keefo/open-plant-pulse/docs/hub.md

# Open Plant Pulse hub

## Goal and priorities

Open Plant Pulse has one hub project: the Python service in [`hub/`](../hub/).
The hub has two primary responsibilities:

1. Run a BLE/BTHome subscriber that continuously listens for nearby sensor
   advertisements, validates them, and stores readings in SQLite.
2. Host a local HTTP server where household users can discover, name, manage, and
   monitor sensors and plants through a web browser.

BLE/BTHome ingestion is the first sensor transport. The HTTP server is still a
core product surface, but it initially serves the hub-owned web application and
only the internal endpoints needed by that application. A stable public HTTP API,
sensor-to-hub Wi-Fi/HTTP reporting, MQTT, and other integrations are lower-priority
follow-up work.

> [!IMPORTANT]
> BTHome advertisements remain one-way telemetry. Firmware 0.3.0 adds a separate,
> bounded connected-BLE service: after the next report, the hub can send plant name,
> room, and reporting interval and verify them by read-back. The prototype service
> is unauthenticated and must not be treated as secure provisioning.

The checked-in vertical slice serves a standard-library HTTP dashboard. It also
includes a Bleak BTHome subscriber,
stable sensor-owned identity, report deduplication, deterministic replay, explicit
SQLite migrations, partial-source storage, and separate scanner/database health.
These paths are host-tested with captured advertisements. The browser now includes
hub health, an unclaimed-sensor inbox, an enrolled fleet overview, sensor-scoped
monitoring, and hub-owned management workflows. CoreBluetooth discovery and scanner
startup have been exercised on macOS; physical BTHome reception and Linux remain
unvalidated.

## Target architecture

```mermaid
flowchart LR
    Probe[RS485 soil probe] --> Sensor[Battery sensor node]
    Air[SHT45 air sensor] --> Sensor
    Sensor -->|BTHome v2 advertisements| BLE[Hub BLE subscriber]
    BLE --> Ingest[Ingestion and enrollment]
    Ingest --> DB[(SQLite)]
    DB --> Web[Local HTTP server and web UI]
    User[Household user] <-->|manage and monitor| Web
    Sensor -.->|same BTHome advertisements| HA[Home Assistant]
    DB -.->|later MQTT bridge| HA
    DB -.->|later public HTTP API| Clients[External clients]
```

The hub remains one background service and one operational SQLite database. The
BLE subscriber and HTTP server run independently: a browser or downstream client
failure must not stop collection, and a temporary Bluetooth failure must not make
stored history unavailable.

Reliable BLE ingestion and persistence take priority over dashboard polish,
analytics, public APIs, MQTT, notifications, and other downstream capabilities.
The implementation should extend the current `sqlite3` store and standard-library
`ThreadingHTTPServer` before adding another framework or storage abstraction.

## Technology baseline

| Concern | Baseline | Reason |
| --- | --- | --- |
| Runtime | Python 3.9+ | Supported by the existing package |
| Sensor ingestion | Passive BTHome v2 advertisements over BLE | Low sensor wake-cycle energy and no Wi-Fi association |
| BLE adapter | `bleak` | Already declared; supports macOS CoreBluetooth and Linux BlueZ |
| HTTP service | Python standard-library threaded server initially | Already powers the tested browser slice |
| Store | SQLite through Python `sqlite3` | Embedded, transactional, and already implemented |
| Home Assistant | Direct BTHome first; hub MQTT later | The same broadcast can be heard without coupling HA to the hub |
| Tests | `unittest` baseline; `pytest` development extra | Zero-dependency core checks and optional richer tooling |

The store uses standard-library `sqlite3`; do not introduce asynchronous database
access unless the BLE runtime demonstrates a need for it. Keep Bluetooth callbacks
short: normalize an advertisement and hand it to application/storage code without
blocking the scanner.

## Current development setup

From the repository root:

```sh
python3 -m venv .venv
. .venv/bin/activate
python3 -m pip install -e './hub[dev]'
pytest hub/tests
```

The current contract and hub tests need no installation:

```sh
PYTHONPATH=hub/src python3 -m unittest discover -s hub/tests
```

Run the existing vertical slice:

```sh
PYTHONPATH=hub/src python3 -m open_plant_pulse_hub
```

Visit <http://localhost/>, or the computer's own name such as
`http://imac.local/`. Readings arrive from BTHome sensors in range.

The interface listens on port 80 on every address, over IPv4 and IPv6, so either
family a name resolves to reaches it. It answers only the computer it runs on and
refuses other computers with 403: it has no login, and macOS lets an ordinary
user take port 80 only on every address at once, so the limit is kept per
request rather than by binding to loopback. `--allow-network` lets the household
network in; `--host` and `--port` choose another address or port.

Firmware images are served separately on `0.0.0.0:8081`, because a sensor
downloads an update over the household network and cannot reach loopback. That
server answers one shape of request — `GET /firmware/<sha256>.bin` — and holds
nothing private. `--firmware-host`, `--firmware-port` and `--no-firmware-server`
change or disable it.

### Running as a macOS service

`deploy/launchd/install.sh` installs the hub as a LaunchAgent that starts at
login and restarts if it exits. It runs the checkout it sits in, through an
ad-hoc signed app bundle, `~/Applications/Open Plant Pulse Hub.app`: a bare
launchd process has no code identity for macOS to attribute Bluetooth
permission to, and its scanner then stays `stopped` without an error. The
bundle's main executable is a small compiled launcher (`launcher.c`, built by
the script, so it needs the Xcode command line tools) that runs the hub as its
child: local network privacy, which grow light control needs, refuses every LAN
connection from an app whose main executable is a script, with `No route to
host` and no prompt. The first light command asks for Local Network permission;
it is under System Settings › Privacy & Security › Local Network. Run the
script again after changing the launcher or moving the checkout, since that
re-signs the bundle; `uninstall.sh` removes the agent and the bundle and keeps
the database. Logs go to `~/Library/Logs/open-plant-pulse/`. Python changes
need a restart, `launchctl kickstart -k gui/$(id -u)/com.openplantpulse.hub`;
the page's own files are read from disk on every request and need none.

### Reaching the hub away from home

Use Tailscale Serve rather than opening a port on the router: the interface has
no login, and anyone who reaches it can reconfigure sensors and install
firmware. With Tailscale on the hub computer and on each phone or laptop that
should reach it, `tailscale serve --bg 80` publishes the page at
`https://<computer>.<tailnet>.ts.net` to those devices only, with a certificate
Tailscale renews. Serve relays through the hub computer, so the hub counts every
such request as local and Tailscale's sign-in is the only access control: never
turn on Funnel or a public tunnel without an authentication layer in front, and
never serve the firmware port. A Serve setting belongs to the computer's
Tailscale name; after renaming the computer, run `tailscale serve reset` and
serve again.

The hub exposes these implementation endpoints for its current page:

- `GET /api/health`
- `GET /api/sensors?status=unclaimed|enrolled|archived`
- `GET /api/sensors/<sensor-id>`
- `GET /api/settings`
- `GET /api/readings/latest`
- `GET /api/readings/history`
- `GET /api/care-log`
- `GET /api/raw-reports?sensor_id=<sensor-id>` (temporary debugging surface)
- `PUT /api/sensors/<sensor-id>`
- `PUT /api/sensors/<sensor-id>/name`
- `PUT /api/sensors/profile`
- `PUT /api/settings`
- `DELETE /api/sensors/<sensor-id>`
- `POST /api/sensors/<sensor-id>/archive`
- `POST /api/sensors/<sensor-id>/replace`
- `GET /api/firmware`
- `POST /api/firmware` (the image itself as the request body)
- `POST /api/sensors/<sensor-id>/firmware` (a digest to install, or none to stop)
- `DELETE /api/firmware/<sha256>`

These routes are an internal browser contract, not the promised public HTTP API.
They may evolve as the multi-sensor UI is built. State-changing routes reject a
browser `Origin` that does not match the request `Host`; requests without `Origin`
remain available to local command-line tools. The server binds to loopback unless
`--host` is explicitly supplied. For LAN use, bind to a private interface only,
restrict the port with the host firewall, and do not expose it to the Internet.
Deterministic BLE tests use the advertisement replay adapter with
[`protocol/fixtures/bthome-v3-replay.json`](../protocol/fixtures/bthome-v3-replay.json).

### Native Bluetooth setup

Install the hub in the repository virtual environment before using BLE:

```sh
python3 -m venv .venv
. .venv/bin/activate
python3 -m pip install -e './hub[dev]'
```

On macOS, Bleak uses CoreBluetooth. The first scan should prompt for Bluetooth
access; if access was denied, enable the terminal or packaged hub under **System
Settings → Privacy & Security → Bluetooth**. A future bundled application must
include `NSBluetoothAlwaysUsageDescription` in its `Info.plist`. CoreBluetooth
reports host-scoped UUIDs rather than portable Bluetooth addresses, which is why
the hub does not use them as sensor identity.

On Linux, Bleak communicates with BlueZ over the system D-Bus. Ensure BlueZ is
installed, the Bluetooth service and adapter are enabled, and the service account
can access the system D-Bus and BlueZ discovery APIs. Do not run the hub as root as
a substitute for correct service permissions. Container or user-namespace
deployment needs explicit D-Bus and adapter access and remains unvalidated.

Start the hub and inspect scanner/database state independently:

```sh
open-plant-pulse-hub
curl --fail --silent http://localhost/api/health
```

`scanner.status` should become `scanning`; permission or adapter failures appear as
`unavailable` with `last_error`. `last_receive_at` remains null until a supported
`0xFCD2` advertisement has decoded successfully. `database.status` reports SQLite
health separately. Use `--no-ble` only when intentionally disabling collection.

## BLE/BTHome subscriber design

### Scan behavior

The subscriber must:

- use observation-only scanning for telemetry; Bleak's active discovery mode remains
  enabled so the `sensor-<DEVICE_ID>` local-name scan response is available on macOS
  and Linux;
- filter service data for BTHome UUID `0xFCD2` in the discovery callback before
  decoding; do not use a scanner-level service UUID filter because CoreBluetooth
  suppresses the sensor's valid service-data-only advertisements when it is set;
- accept only contract-v3 packets: BTHome v2 service data with unencrypted
  device info and the packet 1, packet 2, or beacon layout;
- record the hub receipt time, source adapter, observed Bluetooth identifier, and
  RSSI when the platform provides them;
- reject malformed or unsupported advertisements without stopping the scan loop;
- reconnect with bounded backoff after adapter loss; and
- expose scanner state and the last successful advertisement time to hub health.

For an enrolled sensor with pending device configuration, the subscriber opens one
bounded GATT connection using the platform-observed identifier, writes the versioned
payload, and reads it back. Matching bytes acknowledge application; connection,
write, or read-back failures remain visible as retrying and are attempted on a later
report. The hub records the sensor's reporting interval only from that matching
read-back; saving a new hub interval leaves the last confirmed sensor interval
unchanged until synchronization succeeds. The hub does not connect when no
configuration is pending and no drain is due.

An enrolled sensor keeps each report in a flash queue until the hub acknowledges
it, and advertises its newest queued report the moment it is made. The hub stores
that report straight from the advertisement, which is what keeps the page fresh at
the reporting interval. The queue itself is moved by a bulk drain (see
[durable delivery](../protocol/README.md#durable-delivery-and-acknowledgement)):
over one bonded connection on the same characteristic the hub writes the drain
request `20`, reads queue pages (`20`, a count of up to eight, then each report's
ID and its two advertised packets), stores every report through the same
ingestion path, duplicate and conflict rules as advertised packets, writes the
cumulative acknowledgement `21` plus the last stored report ID (unsigned 32-bit
little-endian), and repeats until a page is empty, then writes the end token
`22`. Drained packets appear in the raw report log with source adapter
`bleak-drain`, the drain time as receipt time and the connection's identifier.

A drain pauses the sensor's advertising for a couple of seconds, so it is the
background guarantee rather than the freshness path. On hearing a packet of a
report that is not yet acknowledged, from a sensor it owns, the subscriber drains
when:

- it has not drained that sensor since the hub started;
- a report ID between the last acknowledged report and this one is not held
  complete, meaning a report was missed over the air; or
- 30 seconds (`DRAIN_INTERVAL_SECONDS`) have passed since the sensor's last
  successful drain.

That decides whether a drain is due, not when it starts. A due drain waits until
the report just heard is complete (both packets stored), which is the start of
the quiet part of the sensor's reporting cycle: the connection then pauses
advertising after a fresh report was heard instead of across it. If no report
completes over the air within 10 seconds (`DRAIN_DEFER_LIMIT_SECONDS`), it drains
anyway. While a drain waits, configuration, status and update work wait with it
and ride on its connection.

Drains of one sensor never overlap and start at most every two seconds
(`DRAIN_SPACING_SECONDS`), whatever the outcome of the last. A failed drain
(connection error, a refused page) is simply tried again by the next
advertisement. One connection reads at most 16 pages (128 reports), and stops
early if a page begins with a report it has already acknowledged. Pending
configuration, a station status poll and a firmware update command share the drain
connection and go before the drain request; a pending release still goes first,
on its own connection.

A page is decoded strictly: a wrong marker, more than eight reports, truncated or
trailing bytes, a record whose ID is not the one inside its packets, packets that
are not a valid packet 1 and packet 2 pair, or reports out of order refuse the
whole page, acknowledging nothing. A report in conflict, or one with any conflict
logged under its key, is never acknowledged: the acknowledgement stops at the
report before it and the drain ends, though the rest of that page is still
stored. Only 30 seconds later is that sensor drained again, since retrying cannot
change the outcome. `acknowledged_at` on each reading records the latest
acknowledgement that covered it. A forced report is an ordinary report.

A backfilled report can be stored after a newer one, so a sensor's latest reading
is its highest complete report ID, not the row stored last; only readings without
a report ID fall back to storage order.

`bleak` presents platform-specific device identifiers: Linux commonly exposes a
Bluetooth address while macOS exposes a CoreBluetooth UUID. Neither is guaranteed
to be portable across hosts or OS resets. Identity must therefore be an explicit
part of the enrollment design rather than an undocumented use of `device.address`.

Contract v3 uses the complete BLE local name `sensor-<DEVICE_ID>`, where `DEVICE_ID`
is the sensor's immutable 48-bit hardware device ID encoded as 12 lowercase
hexadecimal digits. The advertised name and hub canonical ID both use
`sensor-<lowercase-device-id>`. Earlier name forms are not accepted; a sensor still
using one is reflashed.
This sensor-owned identity survives sensor reset, hub replacement, and changes to
the Linux address or macOS CoreBluetooth UUID. Platform identifiers remain bounded
receive diagnostics only. The identifier is observable and spoofable under the
unencrypted contract.

The first valid supported advertisement may create an **unclaimed** sensor record.
The user then assigns a display name, plant, profile, and room. Unknown BTHome
devices must not silently appear as trusted Open Plant Pulse sensors unless the UI
offers an enrollment window or an allowlist policy.

### Reports, duplicates, and partial advertisements

Contract v3 is defined in [`protocol/README.md`](../protocol/README.md). A report is
keyed by `(sensor identity, report ID)`, where the report ID is a 32-bit count the
sensor never repeats. A report travels as packet 1 (soil and air measurements,
optional acquisition timestamp) and packet 2 (battery level, voltage
and whether it is charging, soil pH and nitrogen/phosphorus/potassium when
reported, or the report ID alone). The two may
arrive in either order, and the report is complete when both are stored. A reading
is stored, and appears in latest values, history, and care events, when its packet 1
arrives. Packet 2 is kept in `report_packet2` whichever
arrives first, and its values are copied onto the reading when both are present.

A packet whose content matches what is stored for its key and packet kind is a
duplicate: it is logged as such and stores nothing, which is how the sensor's repeated
advertising is absorbed. The same key with different content is a conflict: it is
logged with decode status `conflict` and never overwrites the stored values. The
beacon, the single byte `0x40`, records presence only and stores no reading. The raw
report log records every packet with its report ID and kind.

`observed_at` is the sensor's acquisition timestamp (`0x50`) as RFC 3339 UTC. A report
without one stores `observed_at` as null alongside `received_at`; ranges, calendars,
and journey summaries place such a reading by its receipt time without recording that
as the observation time.

A failed source omits that source's complete object group. Soil requires `0x02`,
`0x2F`, and `0x56`; air requires `0x2E` and `0x45`. The hub stores source
availability with the reading and never fills a missing value from an earlier
report. Incomplete groups are malformed. Contract changes require matching fixtures,
sensor encoder tests, hub decoder tests, and hardware compatibility checks.

### Security and privacy

The current BTHome payload is unencrypted. Anyone in radio range can observe
measurements and device presence, and the hub cannot cryptographically authenticate
the sender. Initial deployment is therefore suitable only for local environmental
monitoring where that exposure is accepted.

Before claiming authenticated or private sensor ingestion, select and test BTHome
encryption/key provisioning or another authenticated transport. Never log keys,
credentials, or complete long-lived identifiers unnecessarily.

## Persistence model

SQLite remains the single source of truth. Add explicit, transactional migrations
instead of modifying the existing version-1 schema in place. The target model
needs at least:

### `sensors`

- internal stable sensor ID;
- enrollment status and chosen identity material;
- display name, room, plant assignment, and profile;
- first/last seen receipt times and latest RSSI;
- transport/contract version and archival state.

### `advertisements`

- sensor ID, report ID, and packet kind (`packet1`, `packet2`, or `beacon`);
- hub receipt time;
- supported BTHome contract version;
- bounded source metadata and decode status (accepted, duplicate, conflict, or
  rejected).

### `readings`

- advertisement ID, sensor ID, and report ID, unique per sensor (null only for
  readings stored before contract v3);
- acquisition time, null when the sensor did not know it, and receipt time;
- available measurements in canonical units, including battery level, voltage and
  `battery_charging` (true or false; null when the report carried no battery and
  for every reading stored before schema version 19);
- explicit source status for partial samples; and
- no fabricated values for unavailable sources.

### `care_events`

- stable event ID and sensor ID;
- type, time, confidence, summary, and bounded changes.

### Grow lights

- `lights`: ID, name, driver kind, and the driver's own settings as JSON;
- `plant_lights`: which plant each light belongs to, at most one;
- `plant_light_schedules`: one daily window per plant, keyed by plant so it
  survives the plant's sensor being replaced;
- `light_events`: the last 200 commands per light and whether each was confirmed.

The hub drives the lights itself, one driver and one worker per light; see
[the grow light proposal](proposals/grow-light-control.md). Only one program may
hold the Neewer GL1C's UDP port 5052, so start the hub with `--no-lights` while
another controller (gl1cd, Neewer Control Center) still has the light, and
`--simulated-lights` to try the pages without hardware.

Retention is indefinite for the prototype. Add backup, export, aggregation, and
retention controls only after representative database growth is measured.

## Household web experience

The HTTP server should make normal use possible without command-line tools.
Deliver the smallest useful multi-sensor workflow in this order:

1. **Hub health:** BLE adapter/scanner state, database state, uptime, and last
   successful receive time.
2. **Sensor inbox:** newly observed, unclaimed Open Plant Pulse devices with a
   deliberate enrollment action.
3. **Fleet page (`/`):** cards showing each sensor's name, stable identifier, last
   report time, and current state.
4. **Sensor detail (`/sensors/<id>`):** monitoring, history, care-event, plant-health,
   and all configuration controls scoped to one sensor. This page also exposes the
   editable hub-requested reporting interval, the read-only interval last confirmed
   from firmware, and pending/applied/retrying delivery state.

The UI must distinguish:

- **fresh**, based on a configured expected advertising/reporting interval;
- **stale**, after a documented grace period;
- **never received** or **source unavailable**; and
- **scanner unavailable**, which is a hub fault rather than proof that every
  sensor is offline.

Configuration controls do not imply an immediate change. The hub stores a desired
revision and sends plant name, room, and reporting interval when the sensor next
reports. Firmware persists an accepted revision and uses its interval for subsequent
reports. Until read-back confirms the desired revision, the UI and freshness logic
continue to use the last confirmed sensor interval. Profile and alert settings remain
hub-only.

### Normalized soil chemistry

The soil probe (ComWinTop NPKPHCTH-S) measures **bulk** electrical conductivity:
the soil, water, and air between its needles together. Plant profile conductivity
ranges describe **pore-water** EC, the soil water on its own, as a drainage or
pour-through test measures it. An airy potting mix reads far lower in bulk than in
its water, so the raw reading cannot be held against the profile range. The hub
therefore estimates pore-water EC from each reading
(`domain/soil_chemistry.py`):

1. compensate the bulk EC to 25 °C at 2 % per °C;
2. find bulk permittivity from the moisture reading by inverting Topp et al.
   (1980);
3. take the permittivity of water at the soil temperature; and
4. apply Hilhorst (2000) with an offset permittivity of 4.1.

The estimate is approximate, roughly ±30–50 % in absolute terms, and reliable as a
trend. Below 20 % moisture the probe's EC reads zero or close to it and there is no
estimate. The probe does not measure nitrogen, phosphorus, and potassium; it derives
them from EC in a fixed ratio, so the page shows them as probe estimates for trend
only, without a target band. Its pH is shown unjudged until it has been checked once
against a strip or kit.

`GET /api/readings/latest` and each sensor's `latest` carry a `chemistry` object
beside the unchanged reading. Its `status` is:

- `current`: the latest complete reading yields an estimate;
- `last_valid`: it does not, usually because the soil is too dry (`too_dry`), so
  the estimate comes from the most recent reading within 30 days that yields one,
  preferring a reading taken 30–60 minutes after a watering the hub detected; or
- `none`: nothing in the last 30 days yields an estimate.

It also gives the rounded `pore_water_ec_us_cm`, the compensated `ec25_us_cm`,
`nutrient_level` (`low`, `ok`, or `high` against the profile's conductivity ideal
range), the `basis` reading (report ID, times, conductivity, moisture, soil
temperature, and whether it followed a watering), and `age_seconds` since that
reading, dated by `observed_at` or, failing that, `received_at`. The page shows the
nutrient level and pore-water EC with the profile's band under soil chemistry, says
what an estimate was worked out from and how old it is, and keeps the measured bulk
EC with the live readings without a band.

The server binds to loopback by default. LAN exposure for household access must be
explicit and documented with host firewall guidance. State-changing browser
routes require same-origin checks and CSRF protection before LAN mode is treated
as production-ready. Internet exposure and cloud accounts are out of scope.

## HTTP scope and priority

### Priority now: hub web application

Maintain only the routes needed to render and operate the local web UI, plus a
small health endpoint for service diagnostics. These endpoints may remain an
internal contract while the domain and multi-sensor workflows stabilize.

### Lower priority: public HTTP API

A versioned public API for external programs is deferred until BLE ingestion,
identity, persistence, and the household UI are reliable. When scheduled, define
read-only sensor/history endpoints first, then authenticated management endpoints,
with pagination, date bounds, request limits, and compatibility policy.

### Lower priority: sensor Wi-Fi/HTTP transport

Sensor-initiated HTTP reporting remains an optional future transport for use cases
that require acknowledged delivery, larger diagnostics, or configuration replies.
It is not on the critical path for the first hub. Do not provision hub URLs or
tokens in production sensor firmware until complete wake-cycle energy, outage,
authentication/TLS, and retry behavior have been measured against BLE.

## Runtime and package structure

Grow toward the following boundaries without rewriting the tested vertical slice:

```text
open_plant_pulse_hub/
├── domain/          Telemetry, plant profiles, freshness, and care rules
├── application/     Enrollment, ingestion, queries, and management use cases
├── ingestion/       BTHome decode, Bleak subscriber, and the replay test adapter
├── adapters/        SQLite, HTTP, Bluetooth platform, MQTT, and OS adapters
└── static/          Local household web application
```

Keep platform Bluetooth code behind an adapter so parsing and ingestion can be
tested with captured advertisements on hosts without BLE hardware. The service
must shut down the scanner, HTTP server, and database cleanly on termination.

## Delivery plan

### Phase 1: Freeze the BLE contract and replay path — complete

- [x] Decide BTHome identity, packet/deduplication, SHT45 semantics, and partial-source
  behavior.
- [x] Add versioned fixtures for valid, duplicate, partial, malformed, unknown-object,
  and multi-sensor advertisements.
- [x] Extend encoder/decoder host tests together.
- [x] Add a deterministic advertisement replay adapter that feeds the same ingestion
  interface as Bleak.

**Exit:** at least three fixture-backed sensors can be replayed repeatedly without
identity collisions, stale-value fabrication, or duplicate durable samples.

**Completed 2026-09-13:** deterministic full-capture replay before and after a
SQLite restart retains four distinct readings across three stable sensor identities.
Duplicate callbacks and repeated captured packets remain diagnostics rather than
durable readings, and unavailable source groups remain null.

### Phase 2: BLE subscriber and persistence — complete with captured evidence

- [x] Implement the Bleak subscriber for BTHome service data.
- [x] Add versioned migrations for sensors, advertisements, readings, and enrollment.
- [x] Persist normalized readings and bounded receive metadata transactionally.
- [x] Recover from malformed advertisements and Bluetooth adapter interruptions.
- [x] Expose scanner/database health independently of sensor freshness.

**Exit:** macOS and Linux tests or captured evidence show continuous collection,
restart recovery, deduplication, and isolation between at least three sensors.

**Completed 2026-09-13 using captured evidence:** the production scanner callback,
queue, ingestion, and SQLite path recovers after an injected adapter interruption
and isolates the same three captured sensors. Migration, restart, deduplication,
malformed-device isolation, bounded diagnostics, and independent health paths are
host-tested. Native scanner startup was exercised on macOS, but physical BTHome
reception, Linux BlueZ permissions, and multi-sensor radio behavior remain pending
hardware validation and are not claimed by this completion status.

### Phase 3: Household management and monitoring server

- Add hub health, sensor inbox, fleet overview, and per-sensor pages.
- Add name, room, plant/profile, thresholds, archive, and replace/merge workflows.
- Add history and care-event views scoped by sensor.
- Keep the HTTP server loopback-only by default; document explicit LAN mode.
- Add browser-route integration tests and responsive desktop/mobile checks.

**Exit:** a household user can enroll, identify, manage, and monitor at least three
BLE sensors through a browser without using the terminal or mixing their data.

**Implementation status:** complete for replayed sensors. Browser routes and store
tests exercise three isolated identities, enrollment, a dedicated fleet page,
sensor-detail deep links, detail-page configuration and deletion, persisted sensor-specific
freshness intervals, and scoped history. Destructive deletion removes readings, care events,
advertisements, and orphaned plant metadata. Responsive layouts are implemented in
CSS; physical multi-sensor and interactive browser checks remain part of hardware
validation.

### Phase 4: Physical BLE and power validation

- Implement the bounded ESP32-C3 BTHome advertising lifecycle and deep sleep.
- Bump `sensor/version.txt`, build with `sensor/firmware/build.sh`, flash with
  `sensor/firmware/flush.sh`, and verify the running version.
- Verify repeated wake/measure/advertise/sleep cycles under normal and degraded
  radio conditions.
- Measure complete-cycle and deep-sleep energy, advertisement reception rate, and
  battery-life estimates at intended reporting intervals.
- Soak the hub and physical sensors for at least 24 hours.

**Exit:** hardware evidence distinguishes build, flash, running-version, BLE
delivery, restart/soak, and power results; none is inferred from another.

**Implementation status:** started. Firmware 0.3.0 includes an opt-in production
lifecycle that takes one fresh SHT45 reading, emits a contract-v2 air-only BTHome
advertisement for a fixed window, stops NimBLE, configures timer wake-up, and enters
deep sleep. With that lifecycle disabled, development firmware remains awake and
uses the latest valid SHT45 sample. An unconfigured development image reports every
five seconds; after configuration, both modes use the persisted interval. The GATT
delivery/read-back path is host-tested and 0.3.0 builds, but has not been flashed or
physically verified. Firmware 0.2.1 was previously flashed and verified. Soil UART
acquisition, verified probe-power control, configuration security/energy, repeated
production cycles, power, and 24-hour soak evidence remain pending.

### Phase 5: Service packaging and resilience

- macOS: done in `deploy/launchd/` (LaunchAgent and signed app bundle, 2026-09-27).
  Linux: add a systemd definition once BlueZ permissions are understood.
- Verify startup after reboot, clean shutdown, migration, backup, and rollback.
- Test LAN dashboard access and firewall instructions on macOS and Linux.
- Document Bluetooth permission and Linux BlueZ requirements.

**Exit:** a clean supported-host install survives reboot and resumes BLE collection
without manual terminal steps.

### Later: public API, integrations, and alternate transport

- Stabilize and version a public read-only HTTP API.
- Add authenticated management API operations only when required.
- Add MQTT discovery/state publishing and native notifications.
- Re-evaluate sensor Wi-Fi/HTTP or a hybrid mode using measured energy, delivery,
  configuration, and security requirements.

## Acceptance criteria for the first hub release

- The hub continuously subscribes to supported BTHome advertisements.
- At least three physical or replayed sensors retain distinct identities and data.
- Duplicate callbacks do not create duplicate stored samples.
- Partial measurements never reuse stale values from an earlier advertisement.
- Readings persist across hub restart in versioned SQLite storage.
- BLE adapter failure is visible and does not make stored history unavailable.
- A household user can enroll, name, assign, archive, and monitor sensors in the
  local browser UI.
- The UI never presents hub-owned metadata changes as sensor configuration.
- HTTP binds to loopback by default and documented LAN mode is explicitly enabled.
- Existing repository checks and schema migration tests pass.

## Decisions still required before the first hub release

Identity, report deduplication, SHT45/partial-source semantics, and initial
unencrypted operation are frozen in protocol contract v3. Remaining decisions and
validation are:

1. complete Bluetooth adapter and permission validation on supported macOS/Linux hosts;
2. verify Home Assistant behavior for the contract-v3 identity, report ID, and
   temperature objects;
3. decide whether authenticated telemetry justifies bind-key provisioning in a later
   encrypted contract; and
4. decide whether future remote configuration justifies connected BLE, Wi-Fi/HTTP, or a
   hybrid transport.
